tybliddell/5780_MiniProject/print_files/images/Complete_connections.jpg

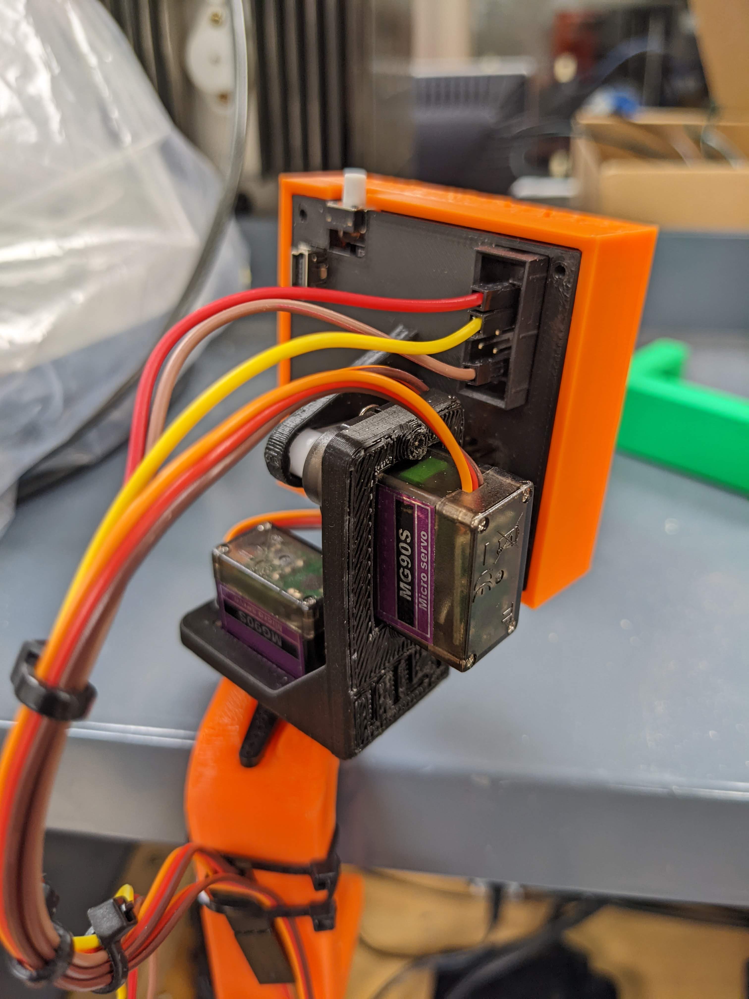
print_files/images/Complete_connections.jpg
