tybliddell/5780_MiniProject/print_files/images/Complete_connections_to_STM32.jpg

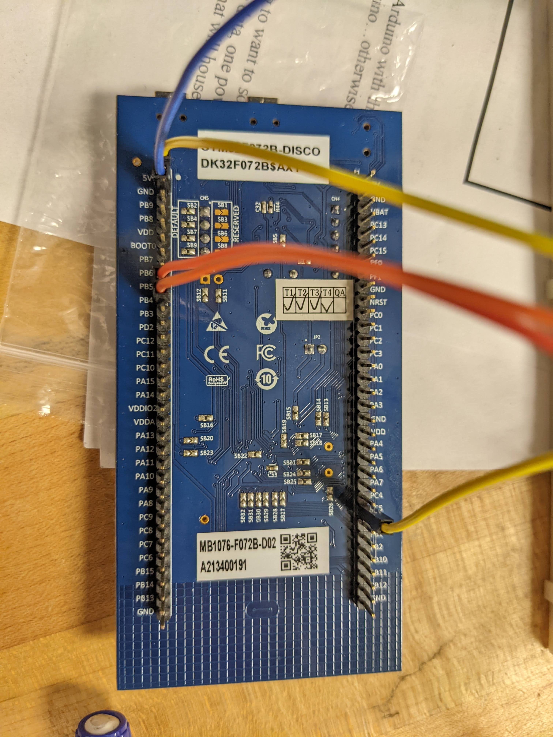
print_files/images/Complete_connections_to_STM32.jpg
