tybliddell/5780_MiniProject/print_files/images/Complete_motor_assembly.jpg

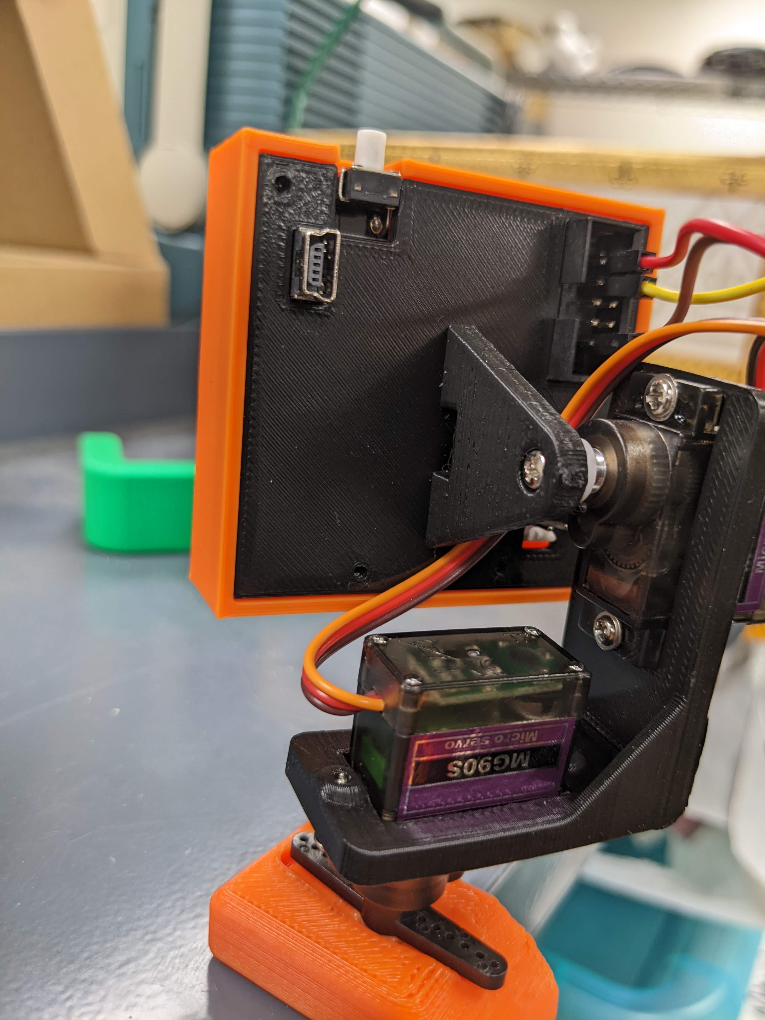
print_files/images/Complete_motor_assembly.jpg
