tybliddell/5780_MiniProject/print_files/images/Complete_Rear_cover.jpg

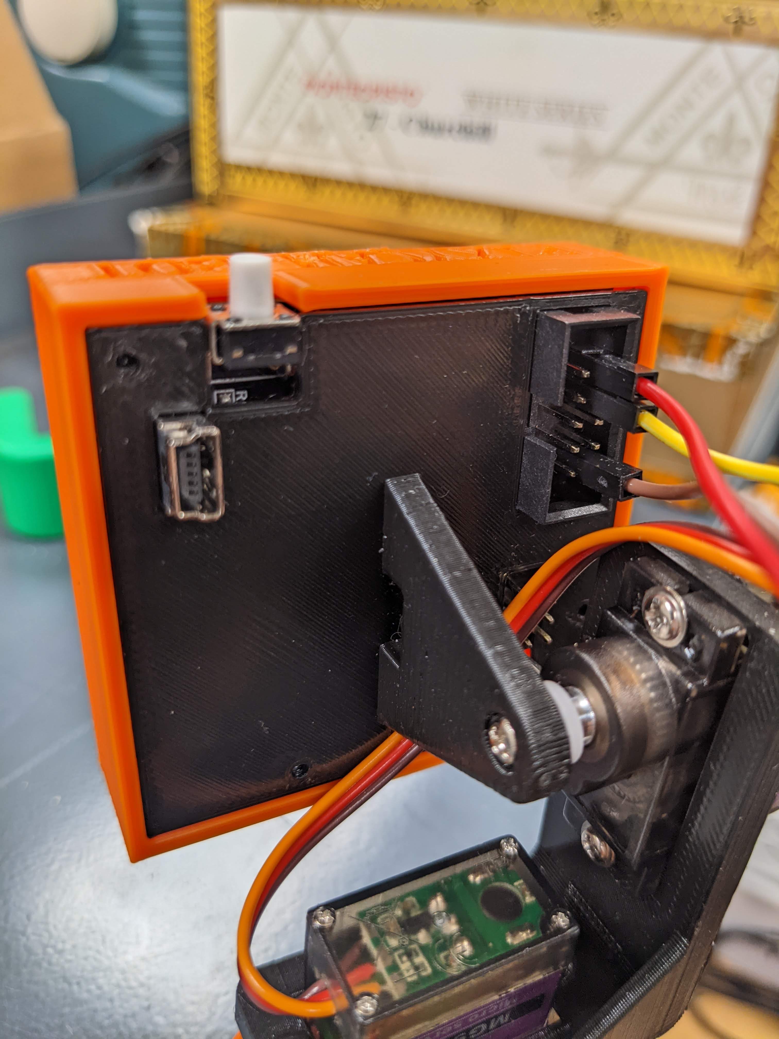
print_files/images/Complete_Rear_cover.jpg
