tybliddell/5780_MiniProject/print_files/images/Inset_lettering_on_housing.jpg

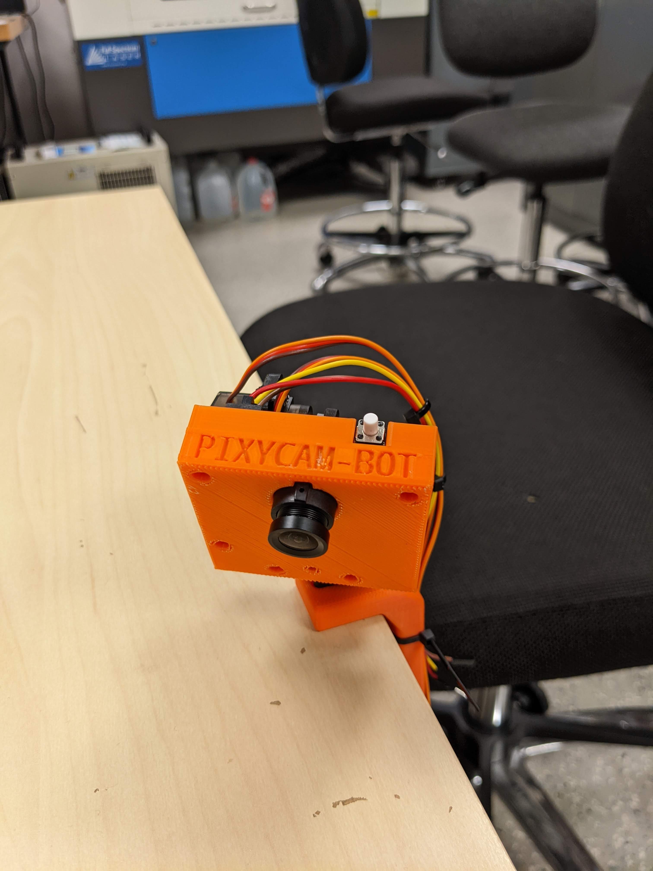
print_files/images/Inset_lettering_on_housing.jpg
