tybliddell/5780_MiniProject/print_files/images/Cable_channel_test.jpg

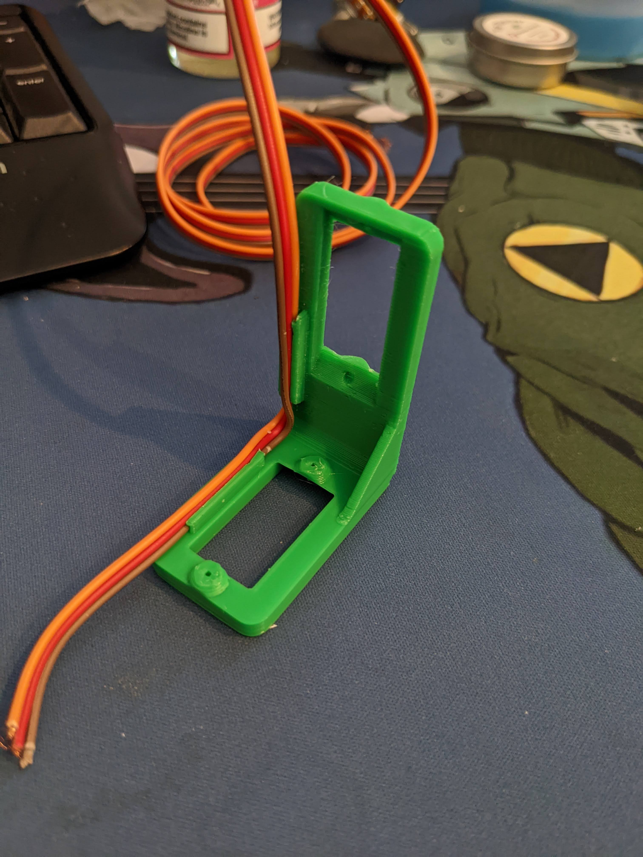
print_files/images/Cable_channel_test.jpg
