tybliddell/5780_MiniProject/print_files/images/Rear_cover_fit_test.jpg

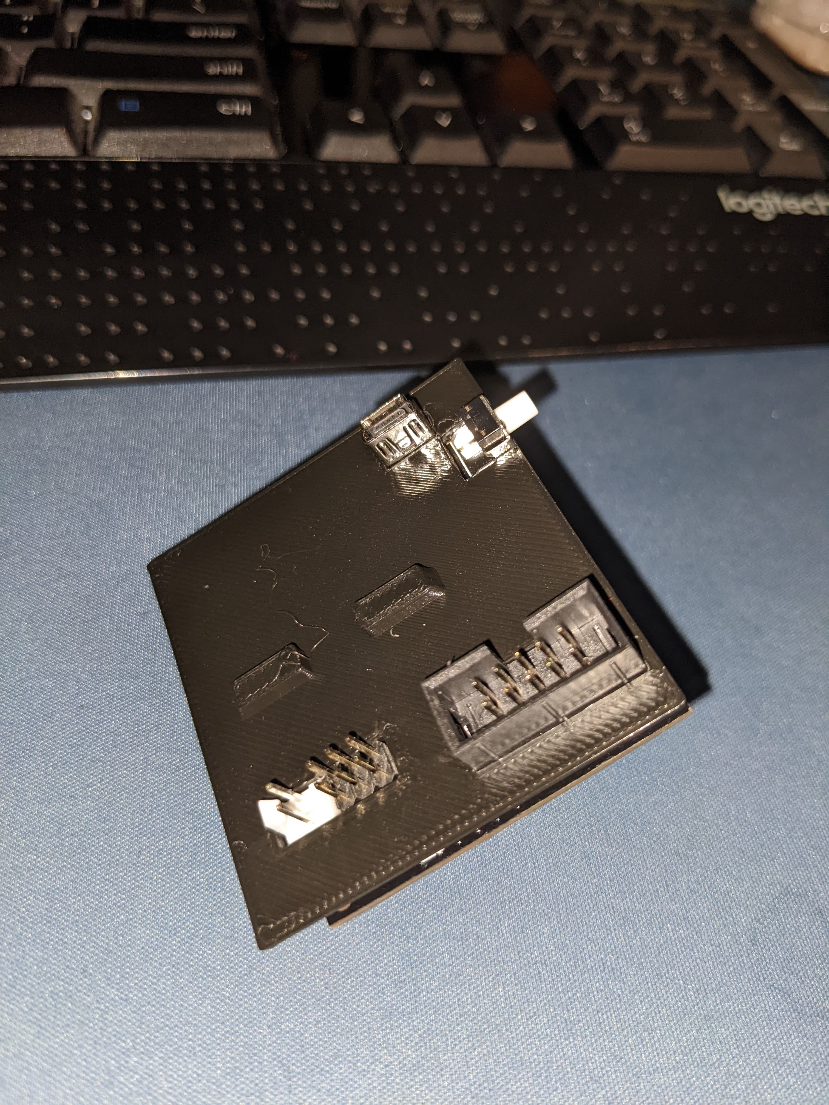
print_files/images/Rear_cover_fit_test.jpg
